dlip/harite/design/key-cirque-40mm.stl

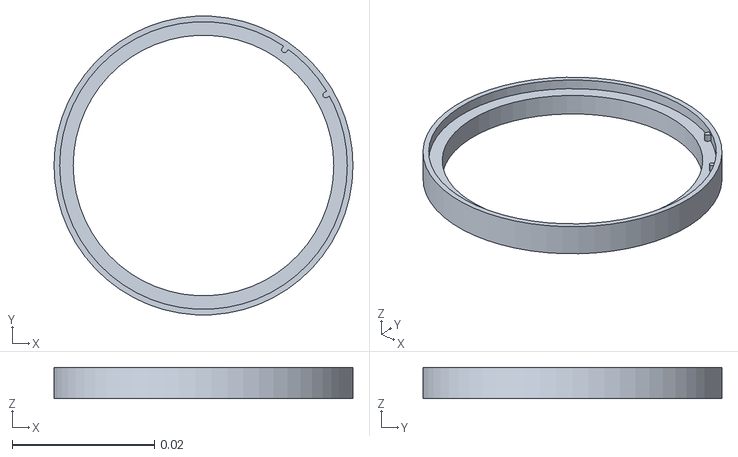
[picture p16: CAD file, 2024-06-02]
design/key-cirque-40mm.stl
0.042 x 0.0419 x 0.0044
