dlip/harite/printables/Cap - Side Guards.stl

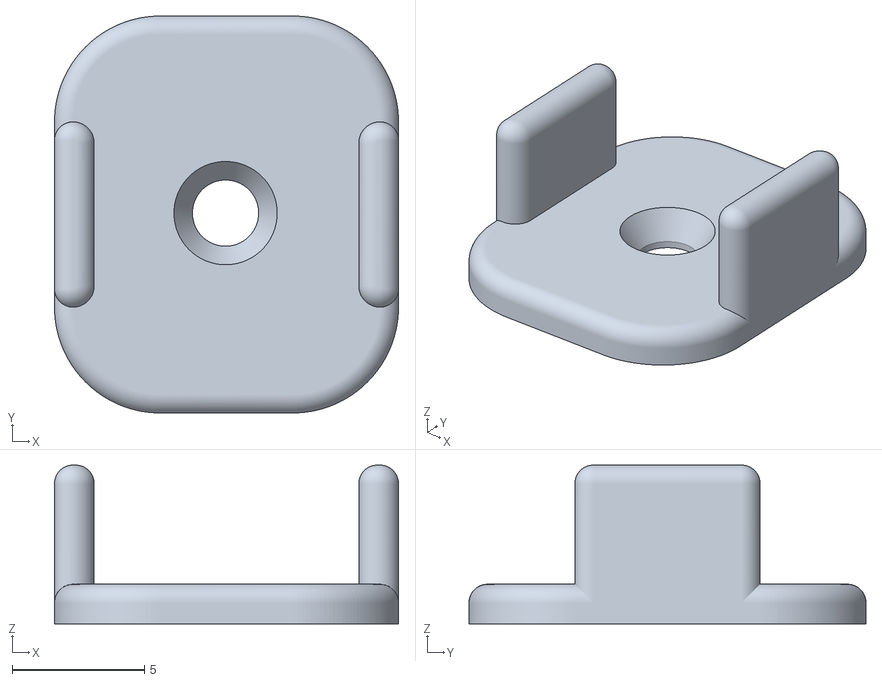
[picture p17: CAD file, 2024-06-29]
printables/Cap - Side Guards.stl
13.0 x 15.0 x 6.00
