dlip/harite/printables/Cap - Rounded Square.stl

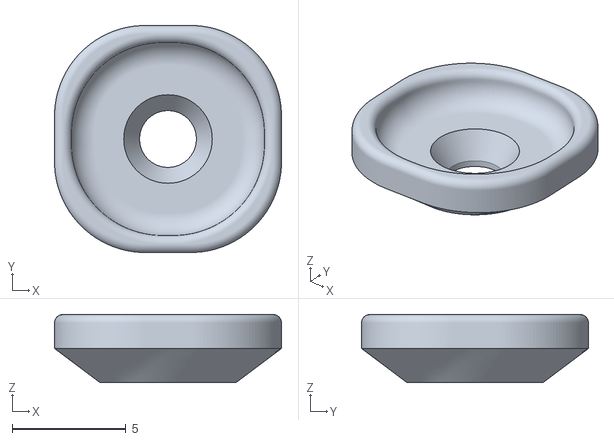
[picture p18: CAD file, 2024-06-29]
printables/Cap - Rounded Square.stl
10.0 x 10.0 x 3.00
