dlip/harite/printables/Stem.stl

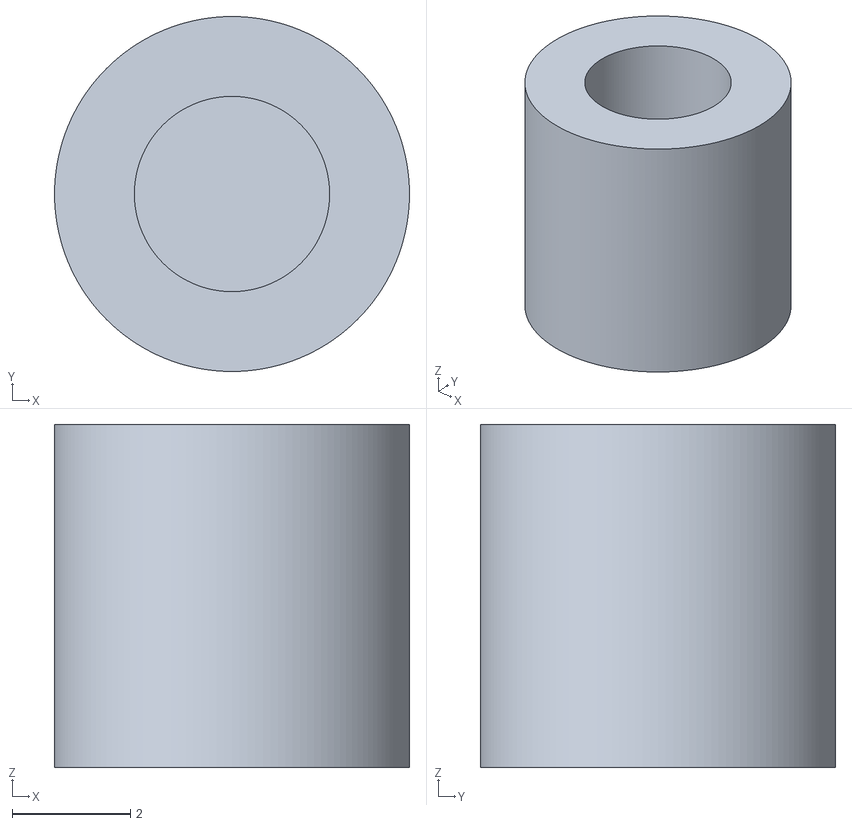
[picture p19: CAD file, 2024-06-28]
printables/Stem.stl
6.00 x 6.00 x 5.80
